ksedgwic/lightning-pos/opennode.ino

// Copyright 2019 Bonsai Software, Inc.  All Rights Reserved.

// OpenNode config
const char* opn_host = "api.opennode.co";
const int opn_port = 443;
String opn_hints = "false";

void opn_rate() {
    // Loop until we succeed
    while (true) {
        Serial.printf("opn_rate updating %s\n", cfg_opn_currency.c_str());
        displayText(10, 100, "OpenNode " + cfg_opn_currency + " ...");

        WiFiClientSecure client;

        while (!client.connect(opn_host, opn_port)) {
            Serial.printf("opn_rate connect failed\n");
            setupNetwork();
        }

        if (cfg_opn_fingerprint.length() > 0 &&
            !client.verify(cfg_opn_fingerprint.c_str(), NULL)) {
            Serial.printf("opn_rate verify failed\n");
            continue;
        }
        
        String url = "/v1/rates";

        client.print(String("GET ") + url + " HTTP/1.1\r\n" +
                     "Host: " + opn_host + "\r\n" +
                     "User-Agent: ESP32\r\n" +
                     "Connection: close\r\n\r\n");

        while (client.connected()) {
            String line = client.readStringUntil('\n');
            if (line == "\r") {
                break;
            }
        }
        String line = client.readStringUntil('\n');

        const size_t capacity =
            169*JSON_OBJECT_SIZE(1) + JSON_OBJECT_SIZE(168) + 3800;
            
        DynamicJsonDocument doc(capacity);
        DeserializationError retval = deserializeJson(doc, line);
        if (retval == DeserializationError::NoMemory) {
            continue;	// retry
        } else if (retval != DeserializationError::Ok) {
            Serial.printf("deserializeJson failed: %s\n", retval.c_str());
            continue; 	// retry
        }
        
        String temp =
            doc["data"][cfg_opn_currency][cfg_opn_currency.substring(3)];
        g_rate = temp.toDouble();
        Serial.printf("1 BTC = %f %s\n",
                      g_rate, cfg_opn_currency.substring(3).c_str());
        return;
    }
}
payreq_t opn_createinvoice() {
    WiFiClientSecure client;

    while (true) {
        Serial.printf("opn_createinvoice %f %lu\n", g_fiat, g_sats);
    
        while (!client.connect(opn_host, opn_port)) {
            Serial.printf("opn_createinvoice connect failed\n");
            setupNetwork();
        }

        if (cfg_opn_fingerprint.length() > 0 &&
            !client.verify(cfg_opn_fingerprint.c_str(), NULL)) {
            Serial.printf("opn_createinvoice verify failed\n");
            continue;
        }
        
        String SATSAMOUNT = String(g_sats);
        String topost =
            "{  \"amount\": \"" + SATSAMOUNT + "\", \"description\": \"" +
            cfg_prefix + cfg_presets[g_preset].title +
            "\", \"route_hints\": \"" + opn_hints + "\"}";
        String url = "/v1/charges";

        client.print(String("POST ") + url + " HTTP/1.1\r\n" +
                     "Host: " + opn_host + "\r\n" +
                     "User-Agent: ESP32\r\n" +
                     "Authorization: " + cfg_opn_apikey + "\r\n" +
                     "Content-Type: application/json\r\n" +
                     "Connection: close\r\n" +
                     "Content-Length: " + topost.length() + "\r\n" +
                     "\r\n" +
                     topost + "\n");

        while (client.connected()) {
            String line = client.readStringUntil('\n');
            if (line == "\r") {
                break;
            }
        }
        String line = client.readStringUntil('\n');

        const size_t capacity =
            169*JSON_OBJECT_SIZE(1) + JSON_OBJECT_SIZE(168) + 3800;
        
        DynamicJsonDocument doc(capacity);
        DeserializationError retval = deserializeJson(doc, line);
        if (retval == DeserializationError::NoMemory) {
            continue;	// retry
        } else if (retval != DeserializationError::Ok) {
            Serial.printf("deserializeJson failed: %s\n", retval.c_str());
            continue; 	// retry
        }
        
        String id = doc["data"]["id"];
        String payreq = doc["data"]["lightning_invoice"]["payreq"];

        // Retry if we don't have a payment request
        if (payreq.length() == 0) {
            Serial.printf("opn_createinvoice failed, retrying\n");
        } else {
            Serial.printf("opn_createinvoice -> %s %s\n",
                          id.c_str(), payreq.c_str());
            return { id, payreq };
        }
    }
}

// Check the status of the payment, return true if it has been paid.
int opn_checkpayment(String PAYID){
    bool saw_error = false;
    WiFiClientSecure client;

    Serial.printf("opn_checkpayment %s\n", PAYID.c_str());

    while (!client.connect(opn_host, opn_port)) {
        Serial.printf("opn_checkpayment connect failed\n");
        saw_error = true;
        setupNetwork();
    }

    if (cfg_opn_fingerprint.length() > 0 &&
        !client.verify(cfg_opn_fingerprint.c_str(), NULL)) {
        Serial.printf("opn_checkpayment verify failed\n");
        return saw_error ? -1 : 0;
    }
        
    String url = "/v1/charge/" + PAYID;

    client.print(String("GET ") + url + " HTTP/1.1\r\n" +
                 "Host: " + opn_host + "\r\n" +
                 "Authorization: " + cfg_opn_apikey + "\r\n" +
                 "User-Agent: ESP32\r\n" +
                 "Connection: close\r\n\r\n");

    while (client.connected()) {
        String line = client.readStringUntil('\n');
        if (line == "\r") {
            break;
        }
    }
    String line = client.readStringUntil('\n');

    const size_t capacity =
        JSON_OBJECT_SIZE(1) + JSON_OBJECT_SIZE(2) + JSON_OBJECT_SIZE(4) +
        JSON_OBJECT_SIZE(14) + 650;
        
    DynamicJsonDocument doc(capacity);
    DeserializationError retval = deserializeJson(doc, line);
    if (retval == DeserializationError::NoMemory) {
        return saw_error ? -1 : 0;
    } else if (retval != DeserializationError::Ok) {
        Serial.printf("deserializeJson failed: %s\n", retval.c_str());
        return saw_error ? -1 : 0;
    }
        
    String stat = doc["data"]["status"];
    Serial.printf("opn_checkpayment -> %s\n", stat.c_str());
    return stat == "paid" ? 1 : (saw_error ? -1 : 0);

}
